leikoilja/muscle-imbalance-detection/analytics/burst.PNG

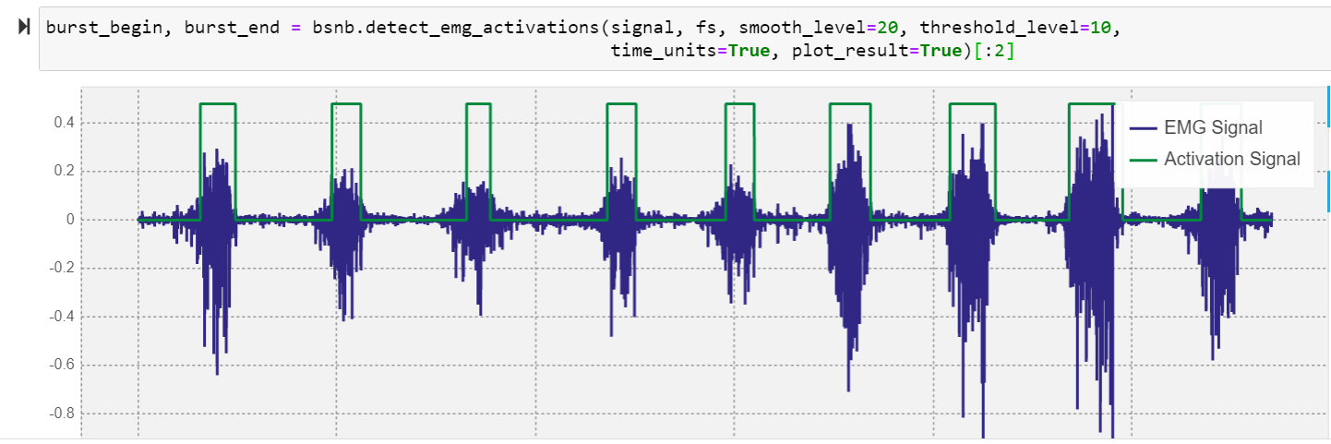
analytics/burst.PNG
