leikoilja/muscle-imbalance-detection/analytics/Rectified signal.png

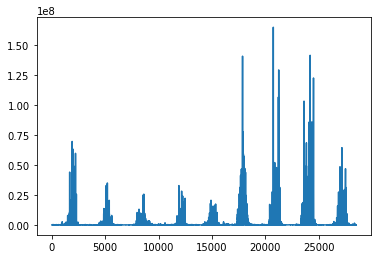
analytics/Rectified signal.png
