leikoilja/muscle-imbalance-detection/analytics/various op.PNG

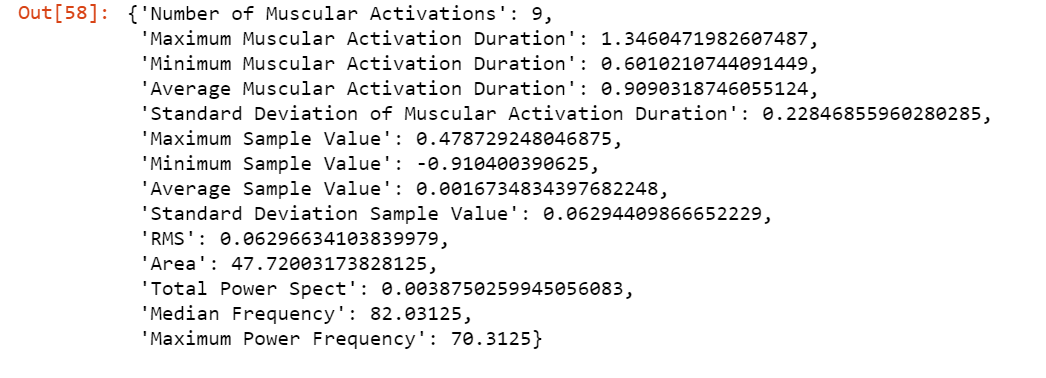
analytics/various op.PNG
